roberto314/Rancho-RT1000-SCSI-8-Bit/pics/IMG_20240324_225930.jpg

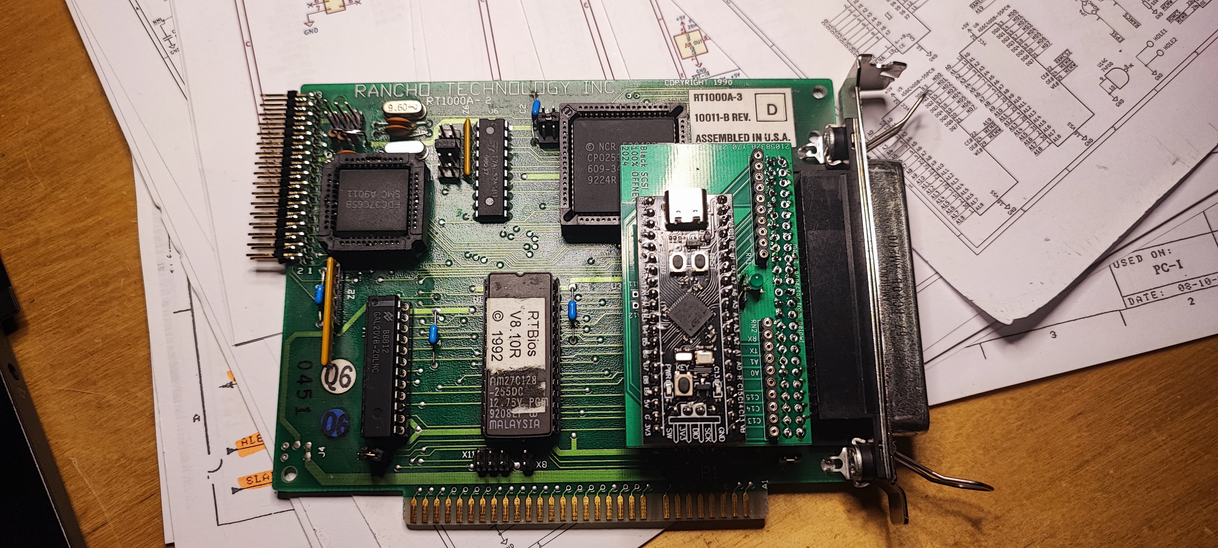
pics/IMG_20240324_225930.jpg
